dita-deb/LocIT/3D Renders/Proposal/ringnecklace.jpg

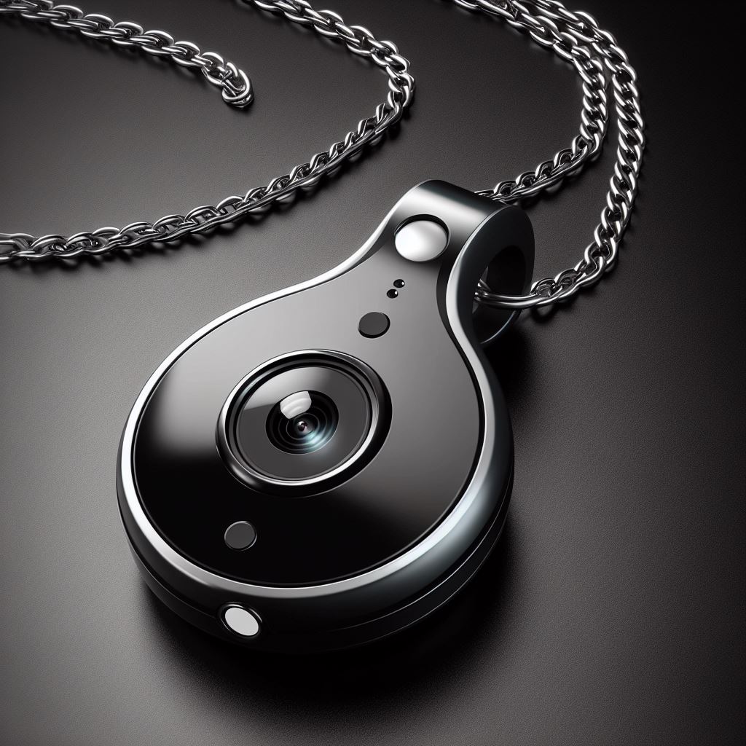
3D Renders/Proposal/ringnecklace.jpg
