dita-deb/LocIT/3D Renders/Locitsketch.JPG

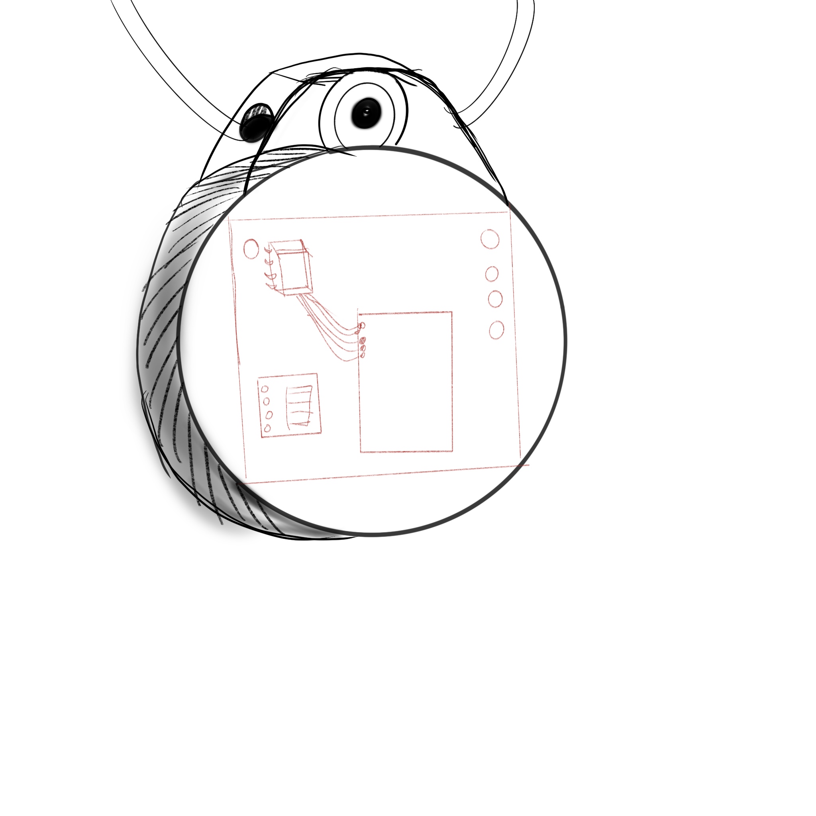
3D Renders/Locitsketch.JPG
