dita-deb/LocIT/3D Renders/Proposal/doorwatchernecklace.jpg

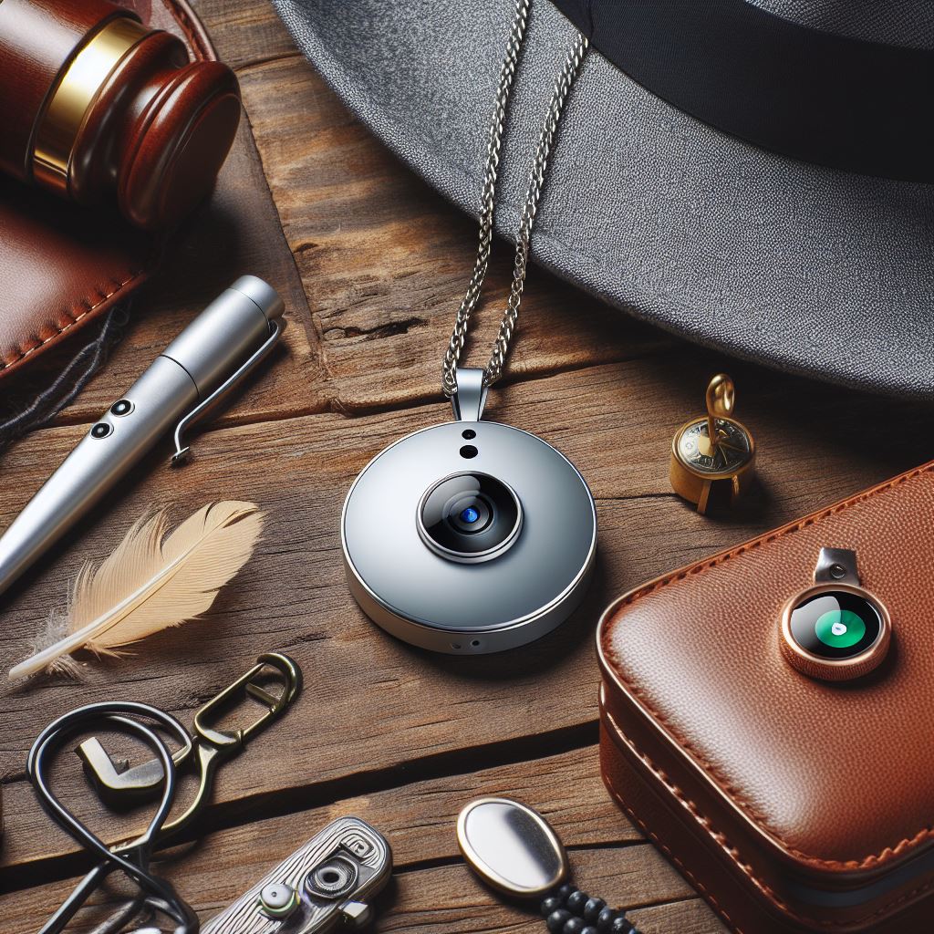
3D Renders/Proposal/doorwatchernecklace.jpg
