dita-deb/LocIT/3D Renders/Proposal/Part Studio 1 (1).png

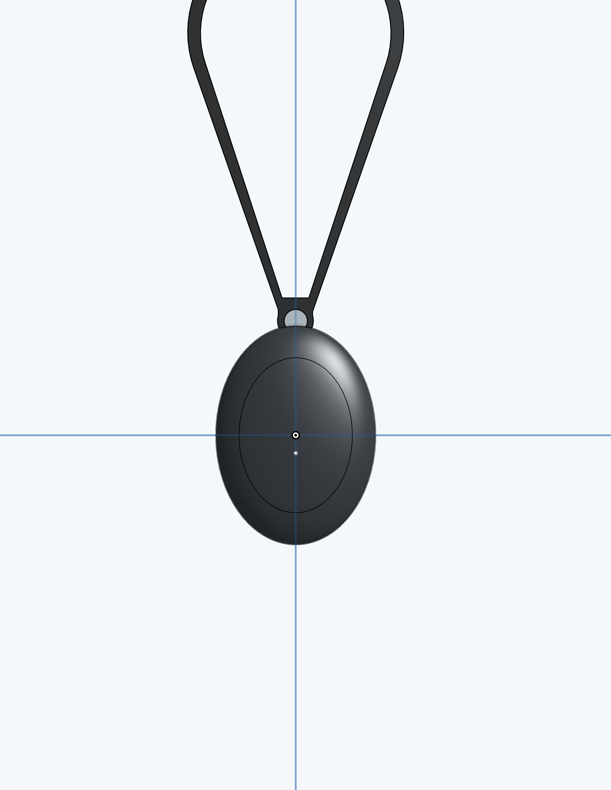
3D Renders/Proposal/Part Studio 1 (1).png
