dita-deb/LocIT/3D Renders/Proposal/Part Studio 1 (5)_1.png

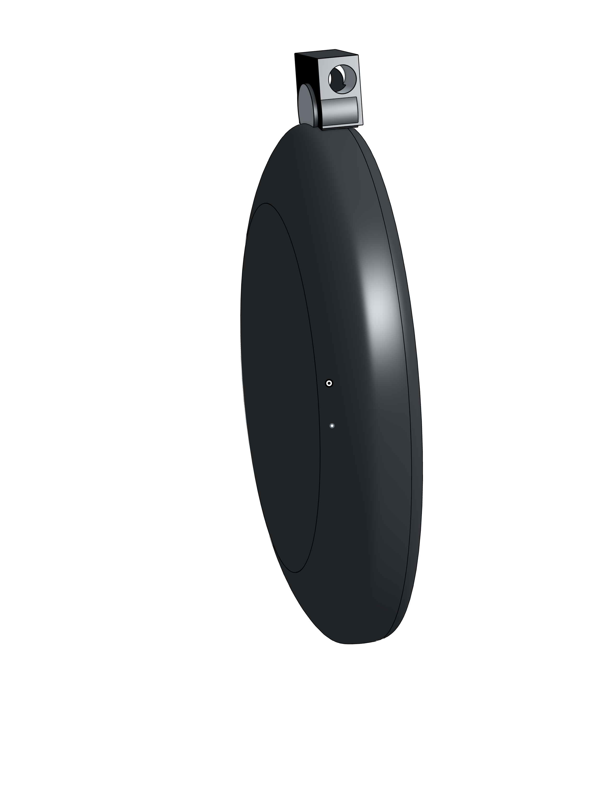
3D Renders/Proposal/Part Studio 1 (5)_1.png
