dita-deb/LocIT/Camera Module/Facial Recognition RPi/face_train.py

import cv2
import numpy as np
from PIL import Image
import os

def get_images_and_labels(path):
    """Load face images and corresponding labels from the given directory path."""
    imagePaths = [os.path.join(path, f) for f in os.listdir(path) if f.startswith("Users-")]
    faceSamples = []
    ids = []

    for imagePath in imagePaths:
        PIL_img = Image.open(imagePath).convert('L')
        img_numpy = np.array(PIL_img, 'uint8')
        id = int(imagePath.split("-")[1])

        faces = detector.detectMultiScale(img_numpy)
        for (x, y, w, h) in faces:
            faceSamples.append(img_numpy[y:y+h, x:x+w])
            ids.append(id)
    return faceSamples, ids

if __name__ == "__main__":
    path = './images/'
    recognizer = cv2.face.LBPHFaceRecognizer_create()
    detector = cv2.CascadeClassifier("haarcascade_frontalface_default.xml")

    faces, ids = get_images_and_labels(path)
    recognizer.train(faces, np.array(ids))
    recognizer.write('trainer.yml')
    print("\n[INFO] {0} faces trained. Exiting Program".format(len(np.unique(ids))))
