dita-deb/LocIT/Camera Module/Facial Recognition RPi/face_taker.py

import numpy as np
import json
import cv2
import os
from picamera2 import Picamera2

def create_directory(directory: str) -> None:
    if not os.path.exists(directory):
        os.makedirs(directory)

def get_face_id(directory: str) -> int:
    user_ids = []
    for filename in os.listdir(directory):
        number = int(os.path.split(filename)[-1].split("-")[1])
        user_ids.append(number)
    user_ids = sorted(list(set(user_ids)))
    max_user_ids = 1 if len(user_ids) == 0 else max(user_ids) + 1
    for i in sorted(range(0, max_user_ids)):
        try:
            if user_ids.index(i):
                face_id = i
        except ValueError:
            return i
    return max_user_ids

def save_name(face_id: int, face_name: str, filename: str) -> None:
    names_json = {}
    if os.path.exists(filename):
        with open(filename, 'r') as fs:
            names_json = json.load(fs)
    names_json[face_id] = face_name
    with open(filename, 'w') as fs:
        json.dump(names_json, fs, ensure_ascii=False, indent=4)

if __name__ == '__main__':
    directory = 'images'
    cascade_classifier_filename = 'haarcascade_frontalface_default.xml'
    names_json_filename = 'names.json'
    create_directory(directory)

    faceCascade = cv2.CascadeClassifier(cascade_classifier_filename)
    picam = Picamera2()
    picam.start()

    count = 0
    face_name = input('\nEnter user name and press <return> -->  ')
    face_id = get_face_id(directory)
    save_name(face_id, face_name, names_json_filename)
    print('\n[INFO] Initializing face capture. Look at the camera and wait...')

    while count < 30:
        frame = picam.capture_array()
        gray = cv2.cvtColor(frame, cv2.COLOR_BGR2GRAY)
        faces = faceCascade.detectMultiScale(gray, scaleFactor=1.3, minNeighbors=5)
        
        for (x, y, w, h) in faces:
            cv2.rectangle(frame, (x, y), (x+w, y+h), (255, 0, 0), 2)
            count += 1
            cv2.imwrite(f'./images/Users-{face_id}-{count}.jpg', gray[y:y+h, x:x+w])
            cv2.imshow('image', frame)
        
        if cv2.waitKey(100) & 0xFF == 27:  # Press Escape to exit
            break

    print('\n[INFO] Success! Exiting Program.')
    picam.close()
    cv2.destroyAllWindows()
