dita-deb/LocIT/Camera Module/Proposal/camera_calibration/parameters.txt

Parameters were computed using the cameracalib.py taken from OpenCV and using 30+ webcam photos of a planar 9x6 chessboard

Attempt 1:


Camera matrix : 

[[1.10481797e+03 0.00000000e+00 9.76862669e+02]
 [0.00000000e+00 1.11775382e+03 5.07678687e+02]
 [0.00000000e+00 0.00000000e+00 1.00000000e+00]]

distorsion coefficients:

[[ 0.13580439 -0.08770944 -0.01913275 -0.00170941 -0.0361747 ]]


Attempt 2:

Camera matrix : 

[[1.09520943e+03 0.00000000e+00 9.80688063e+02]
 [0.00000000e+00 1.10470495e+03 5.42055897e+02]
 [0.00000000e+00 0.00000000e+00 1.00000000e+00]]


dist :

[[ 1.41401053e-01 -2.12991544e-01 -8.88887657e-04  1.03893066e-04
   9.54437692e-02]]


Attempt 3 (laptop camera):

Camera matrix :

[[899.12150372   0.         644.26261492]
 [  0.         899.45280671 372.28009436]
 [  0.           0.           1.        ]]


dist : 

[[-0.03792548  0.09233237  0.00419088  0.00317323 -0.15804257]]
